TreeNewbeer/esp32c6-pico/output/antenna-28mm-comparison.png

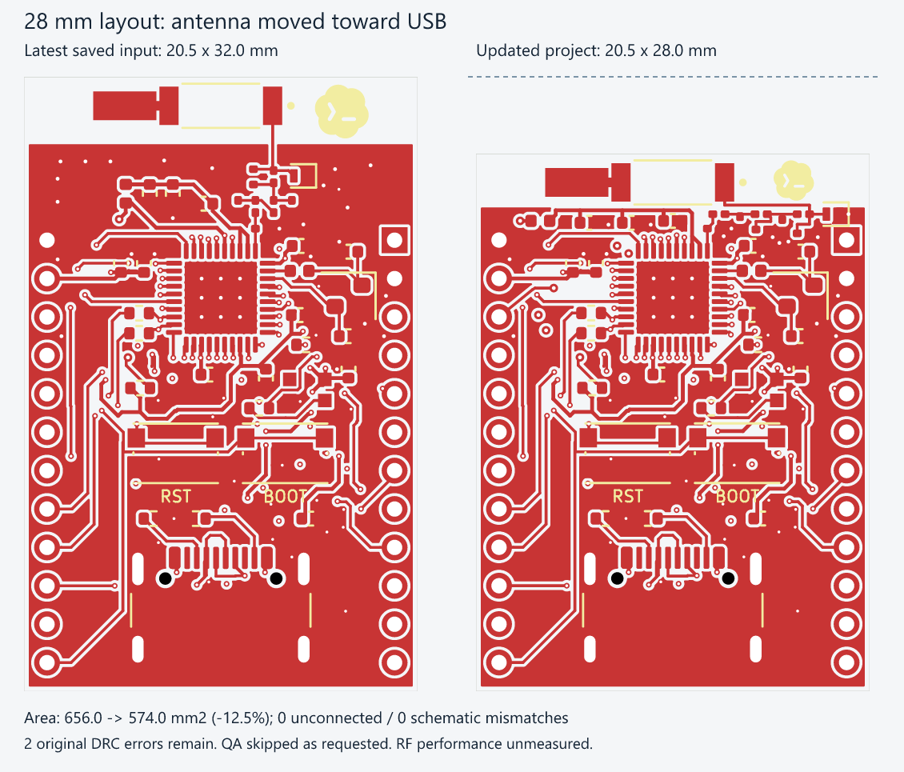
output/antenna-28mm-comparison.png
