TreeNewbeer/esp32c6-pico/output/antenna-layout-comparison.png

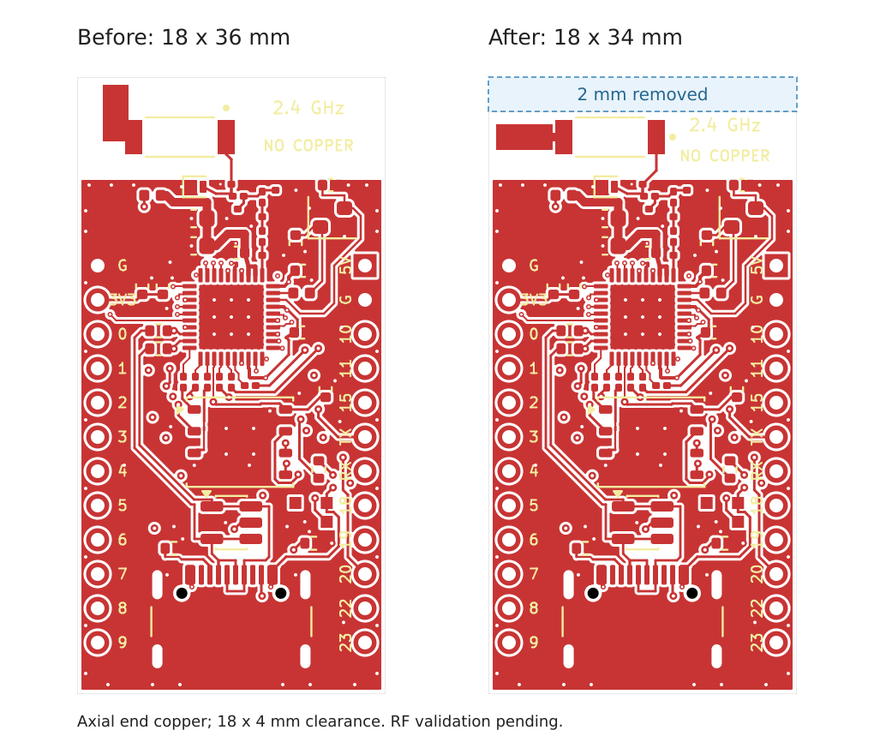
output/antenna-layout-comparison.png
