TreeNewbeer/esp32c6-pico/output/antenna-right-29mm-comparison.png

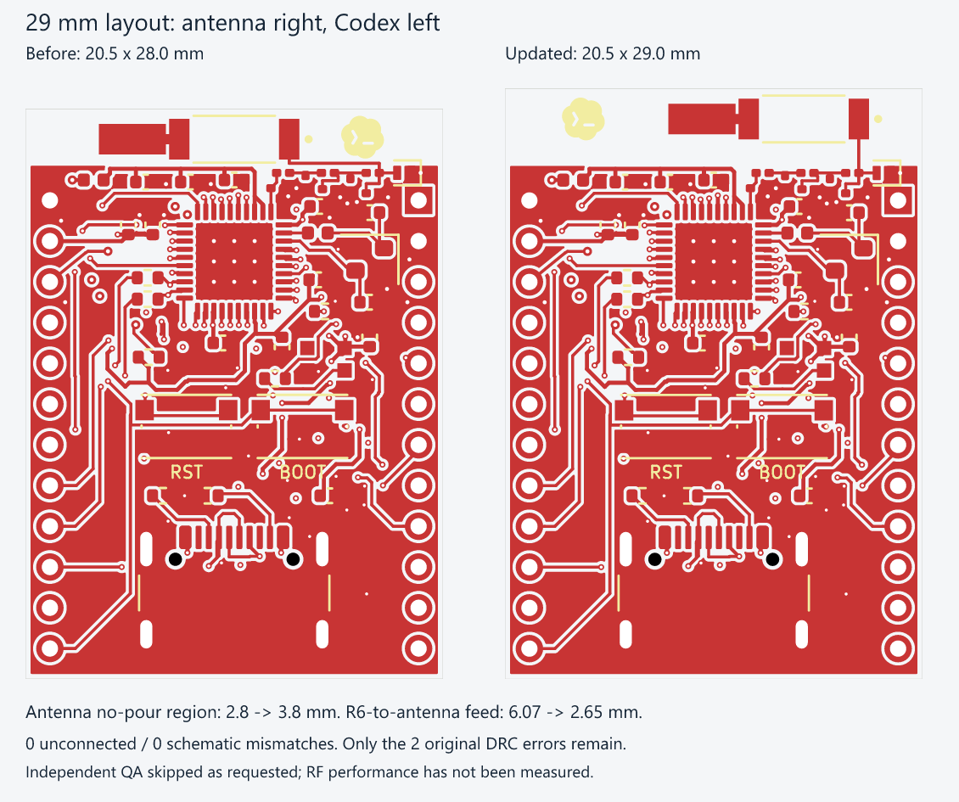
output/antenna-right-29mm-comparison.png
