TreeNewbeer/esp32c6-pico/output/board-3d-bottom.png

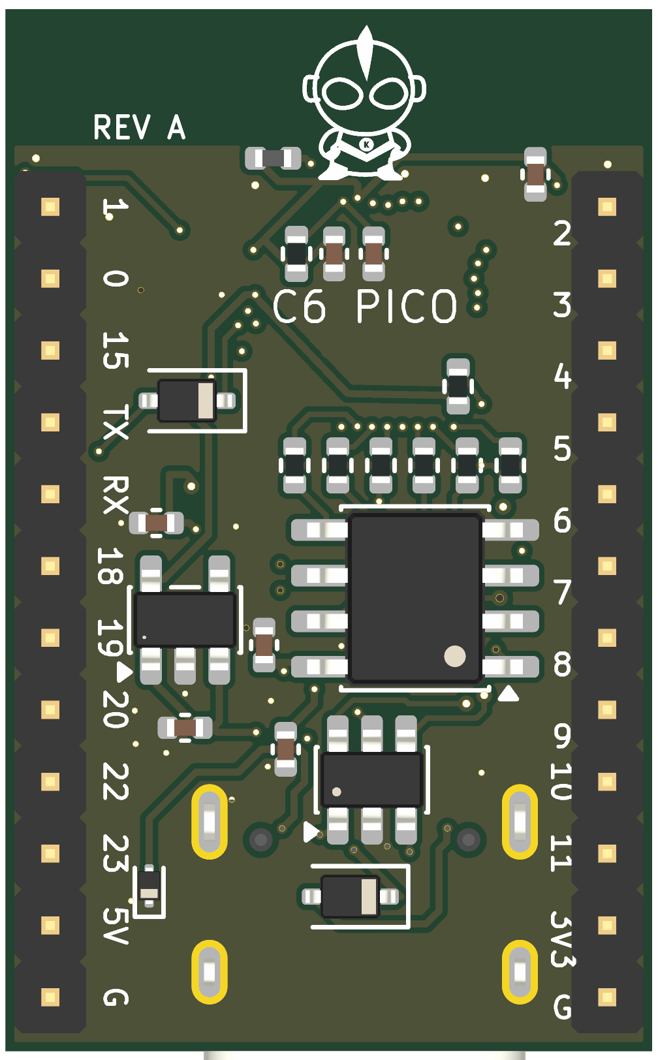
output/board-3d-bottom.png
