TreeNewbeer/esp32c6-pico/output/board-3d-top.png

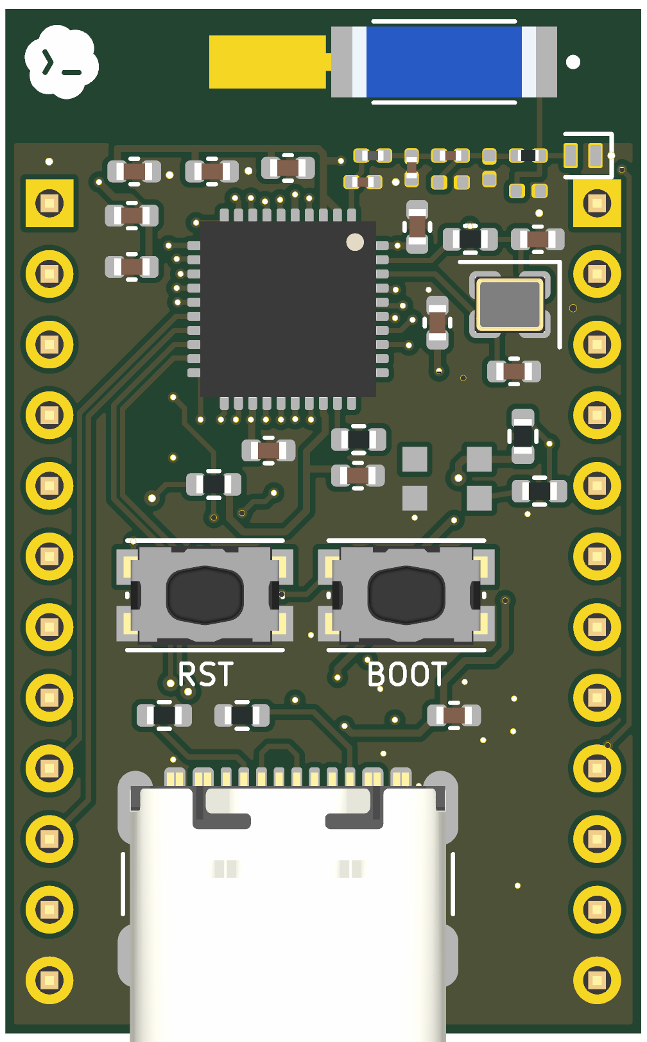
output/board-3d-top.png
