TreeNewbeer/esp32c6-pico/output/crystal-down-headers-comparison.png

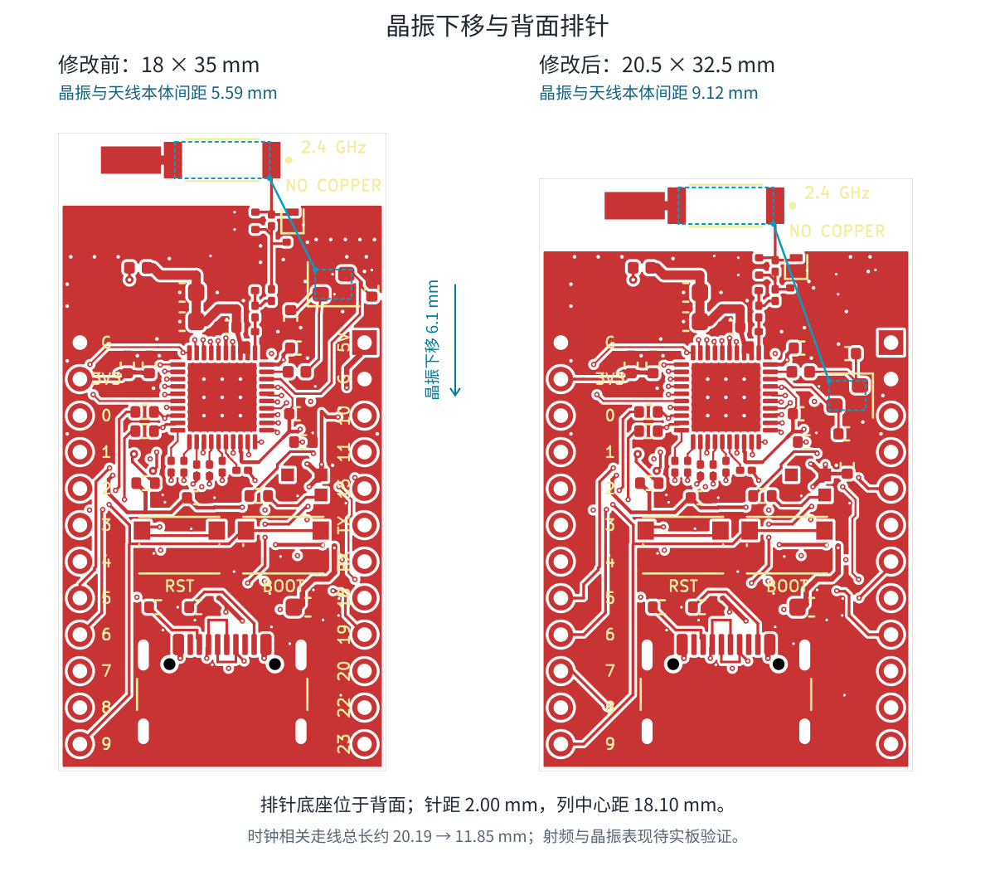
output/crystal-down-headers-comparison.png
