TreeNewbeer/esp32c6-pico/output/crystal-isolation-comparison.png

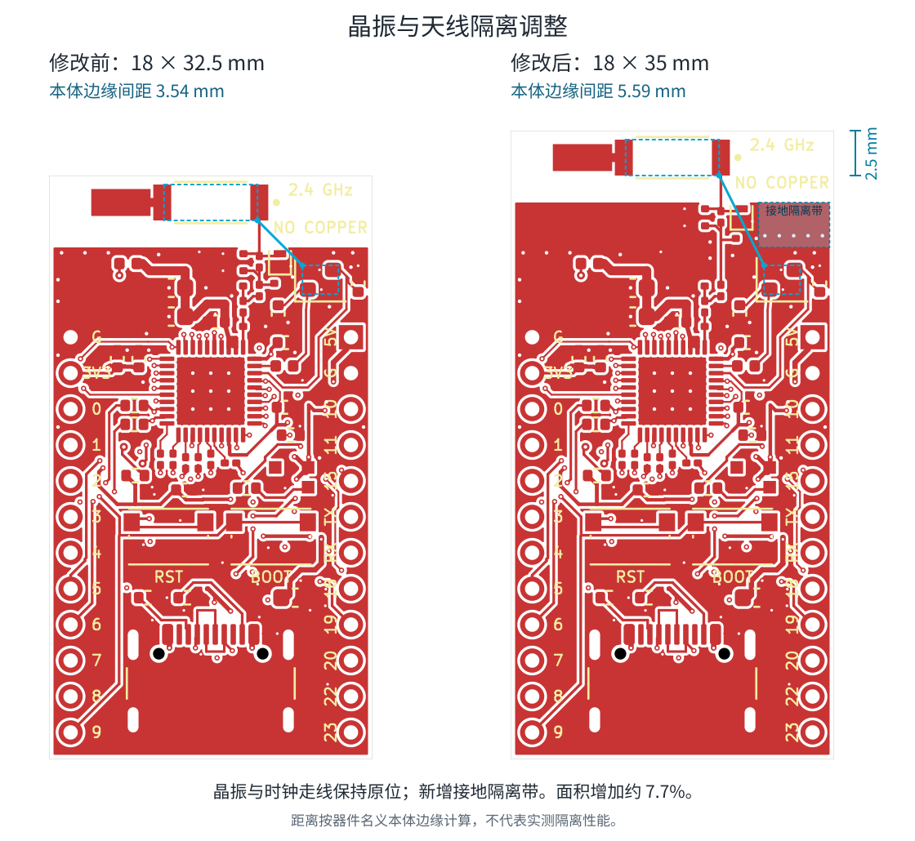
output/crystal-isolation-comparison.png
