TreeNewbeer/esp32c6-pico/output/layout-repack-comparison.png

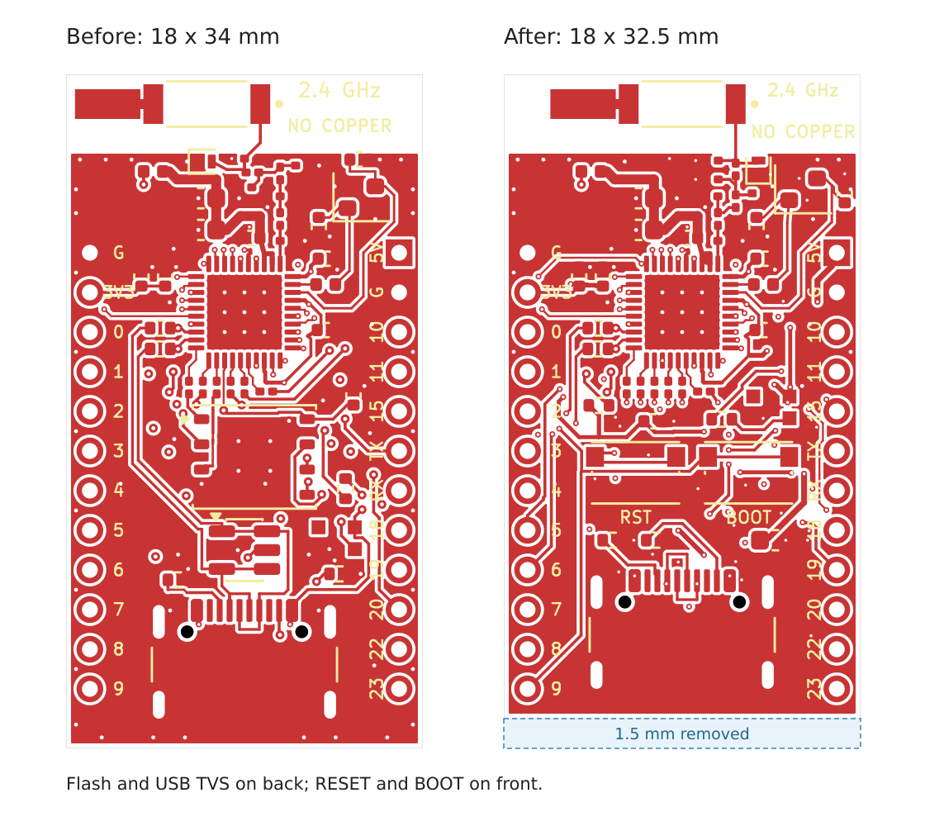
output/layout-repack-comparison.png
