TreeNewbeer/esp32c6-pico/output/pcb-back.png

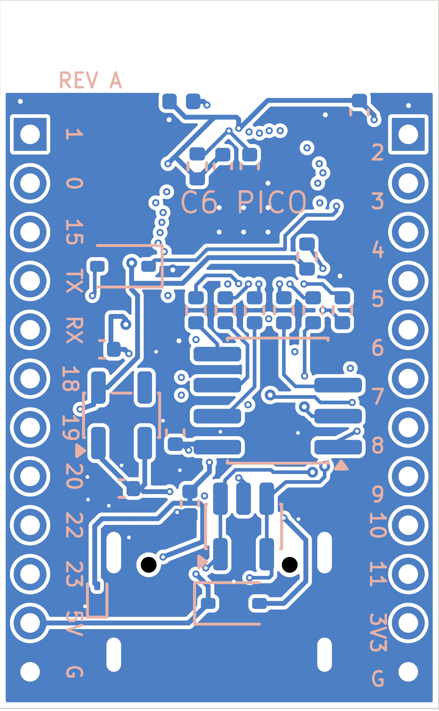
output/pcb-back.png
