TreeNewbeer/esp32c6-pico/output/pcb-front.png

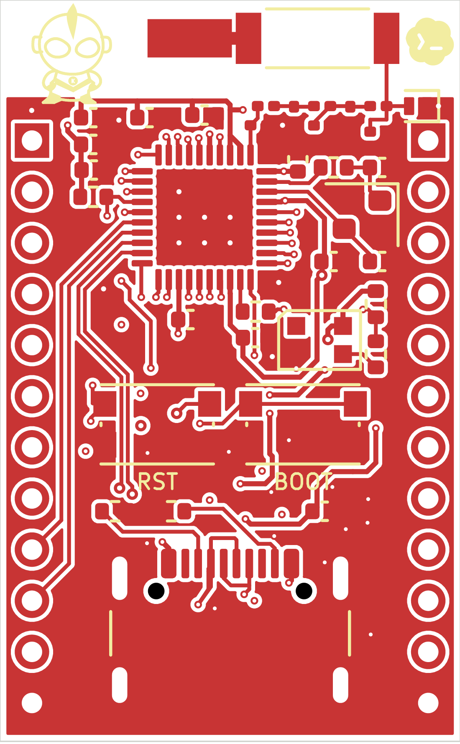
output/pcb-front.png
