TreeNewbeer/esp32c6-pico/output/rgb-diode-comparison.png

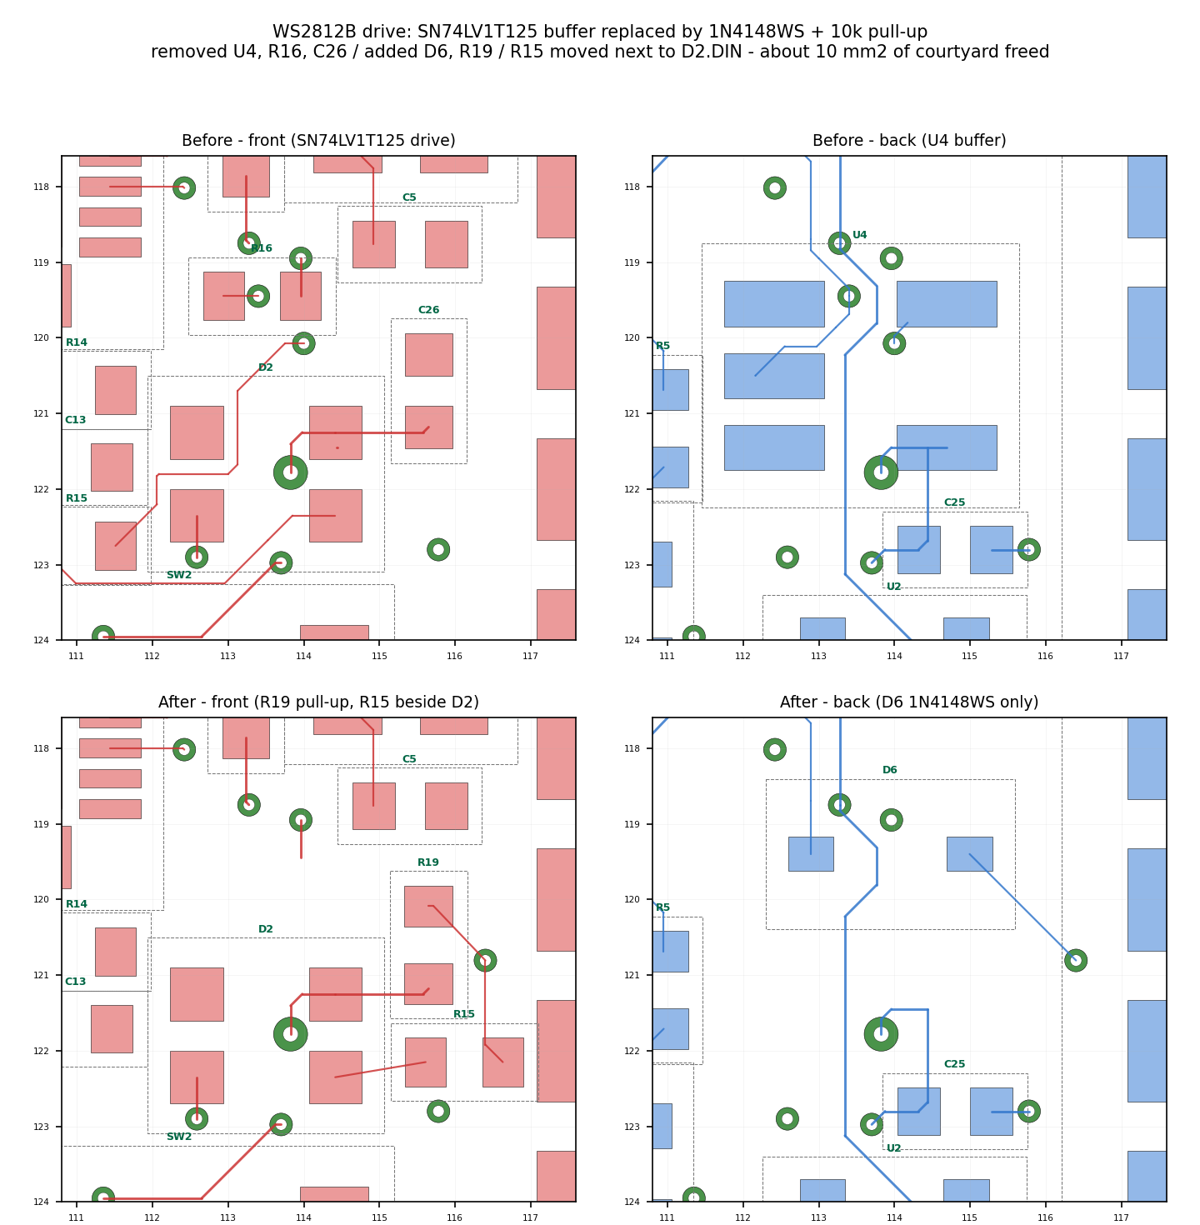
output/rgb-diode-comparison.png
