TreeNewbeer/esp32c6-pico/output/schematic/esp32-c6-pico-Power, USB and interfaces.png

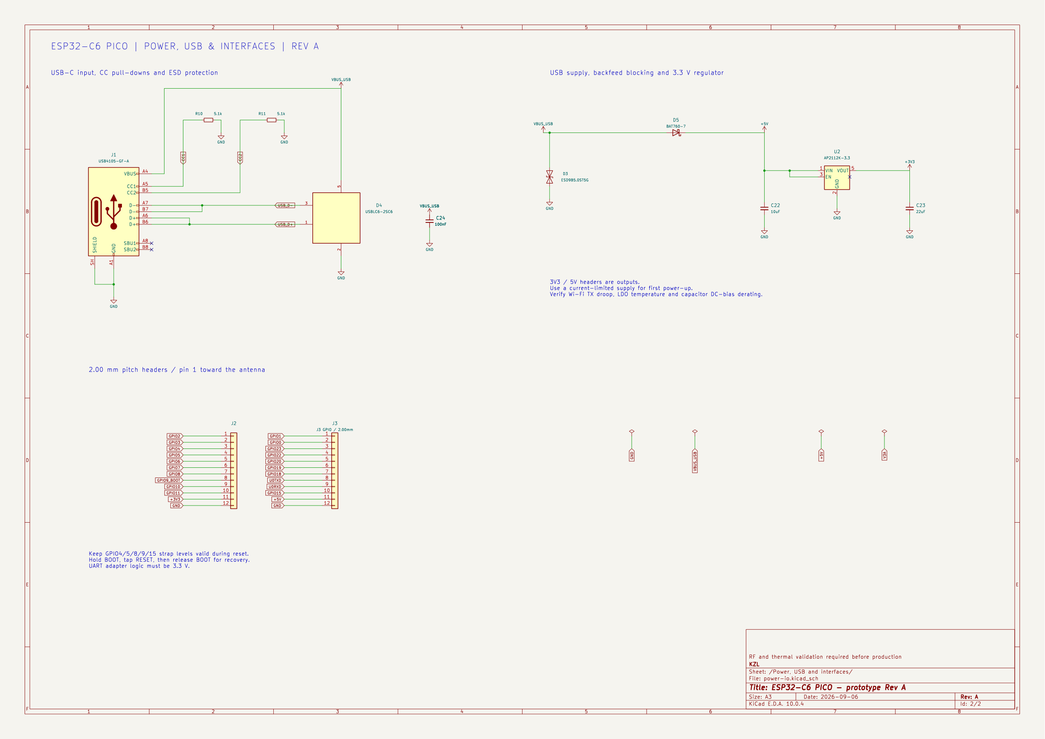
output/schematic/esp32-c6-pico-Power, USB and interfaces.png
