TreeNewbeer/esp32c6-pico/output/schematic/esp32-c6-pico.png

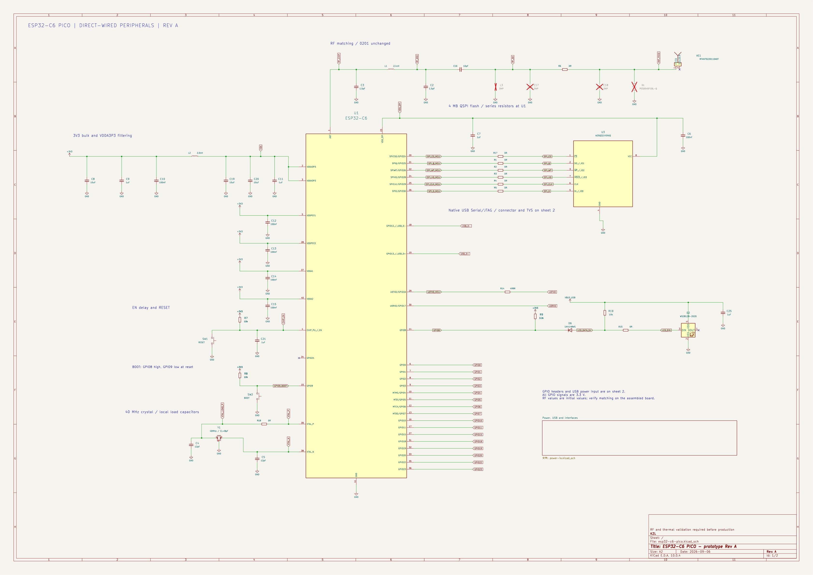
output/schematic/esp32-c6-pico.png
