TreeNewbeer/esp32c6-pico/output/schematic/rgb-gpio8.png

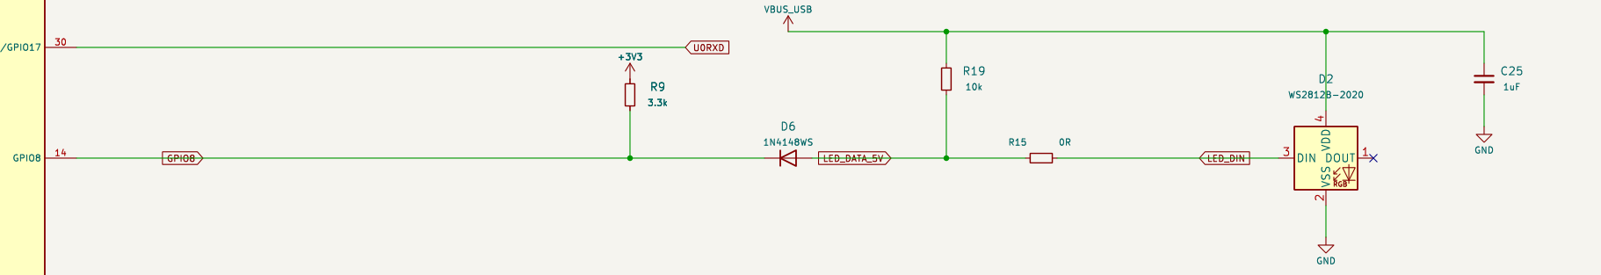
output/schematic/rgb-gpio8.png
