TreeNewbeer/esp32c6-pico/output/usb-buttons-centered-comparison.png

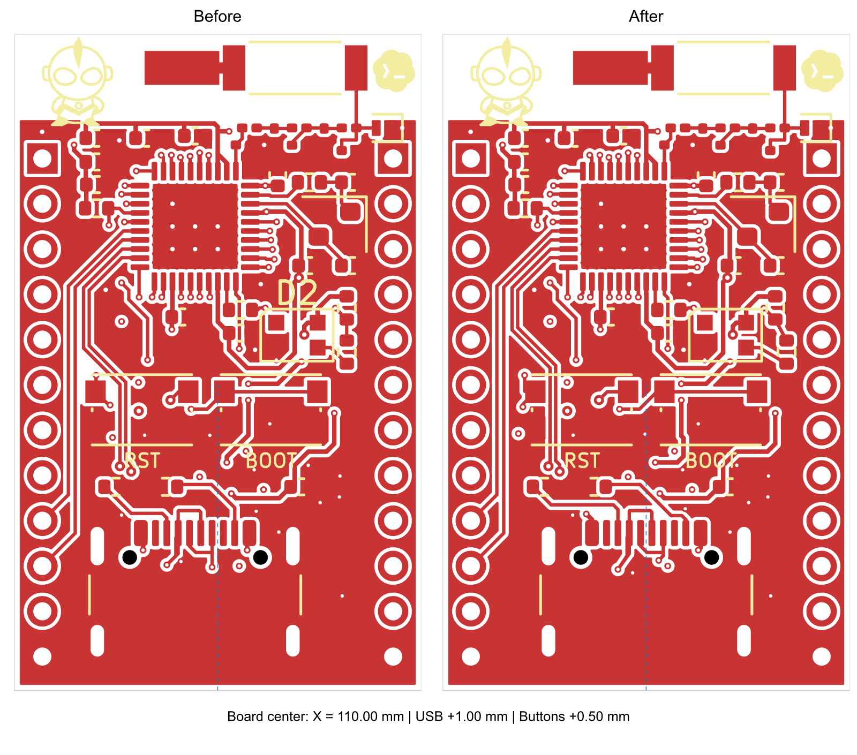
output/usb-buttons-centered-comparison.png
