TreeNewbeer/esp32c6-pico/output/usb-routing-comparison.png

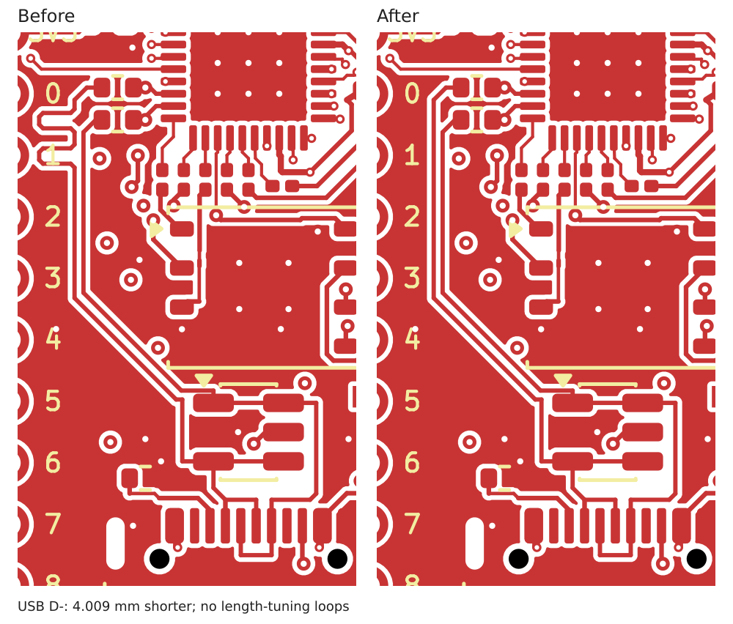
output/usb-routing-comparison.png
