TreeNewbeer/esp32c6-pico/output/width-20mm-comparison.png

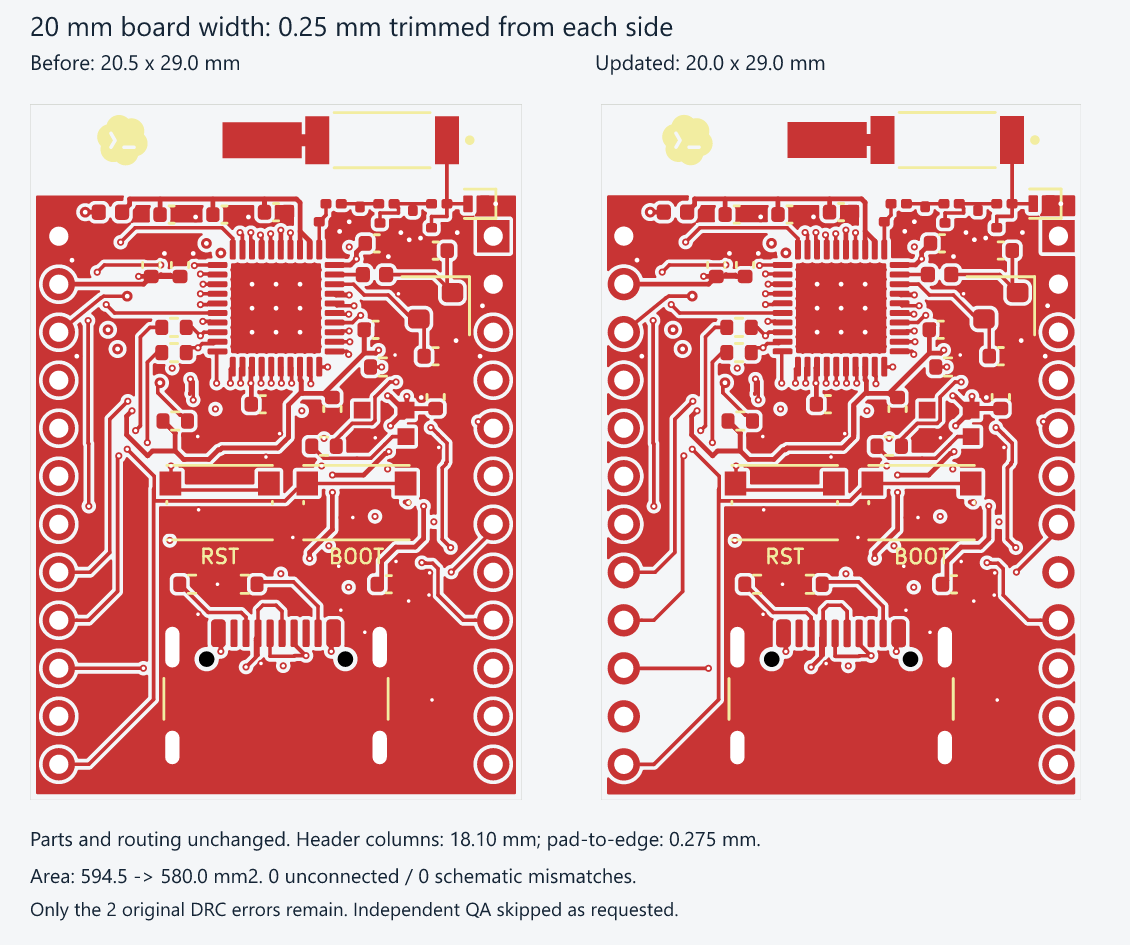
output/width-20mm-comparison.png
