TreeNewbeer/esp32c6-pico/output/assembly-back.png

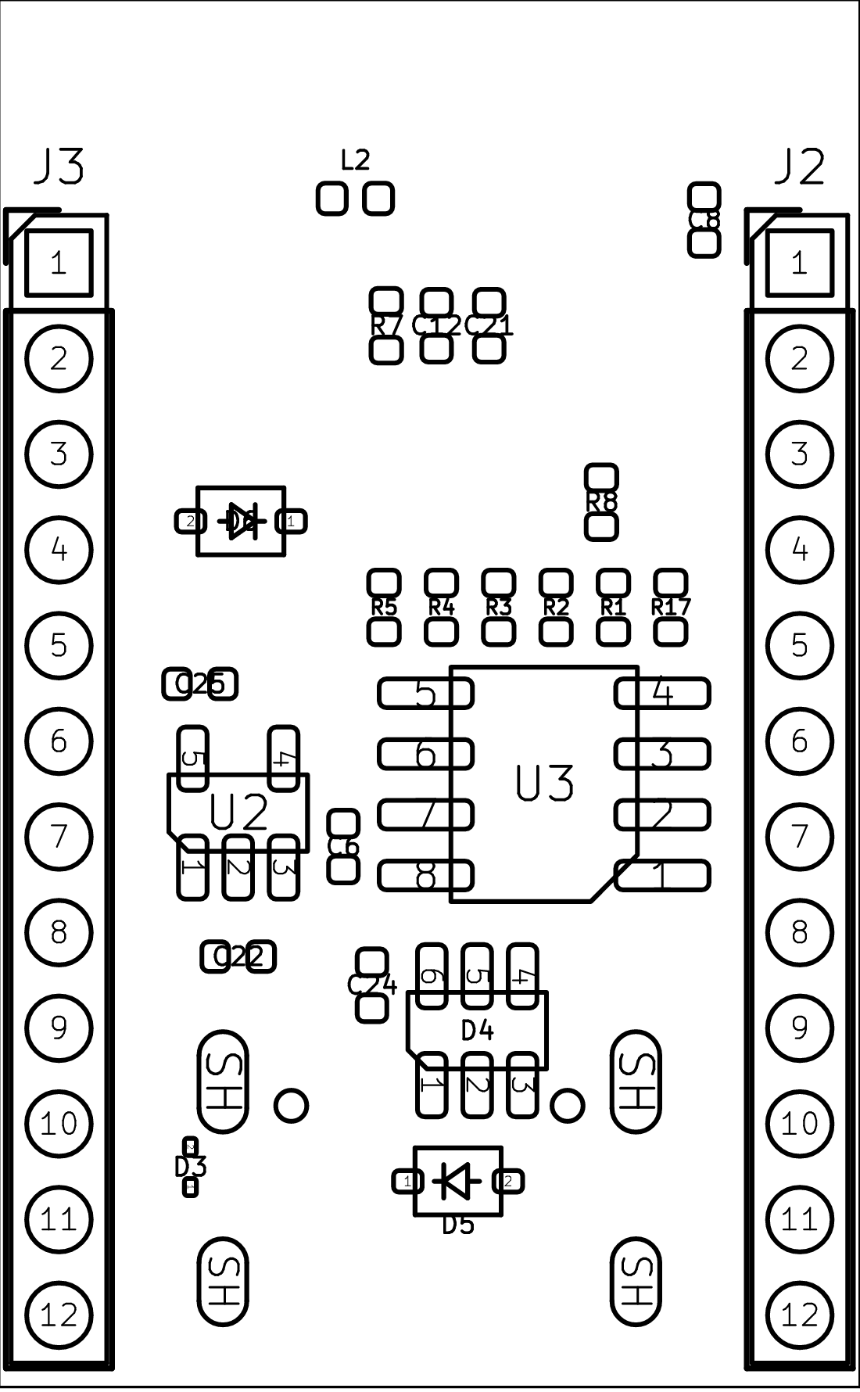
output/assembly-back.png
