TreeNewbeer/esp32c6-pico/output/assembly-front.png

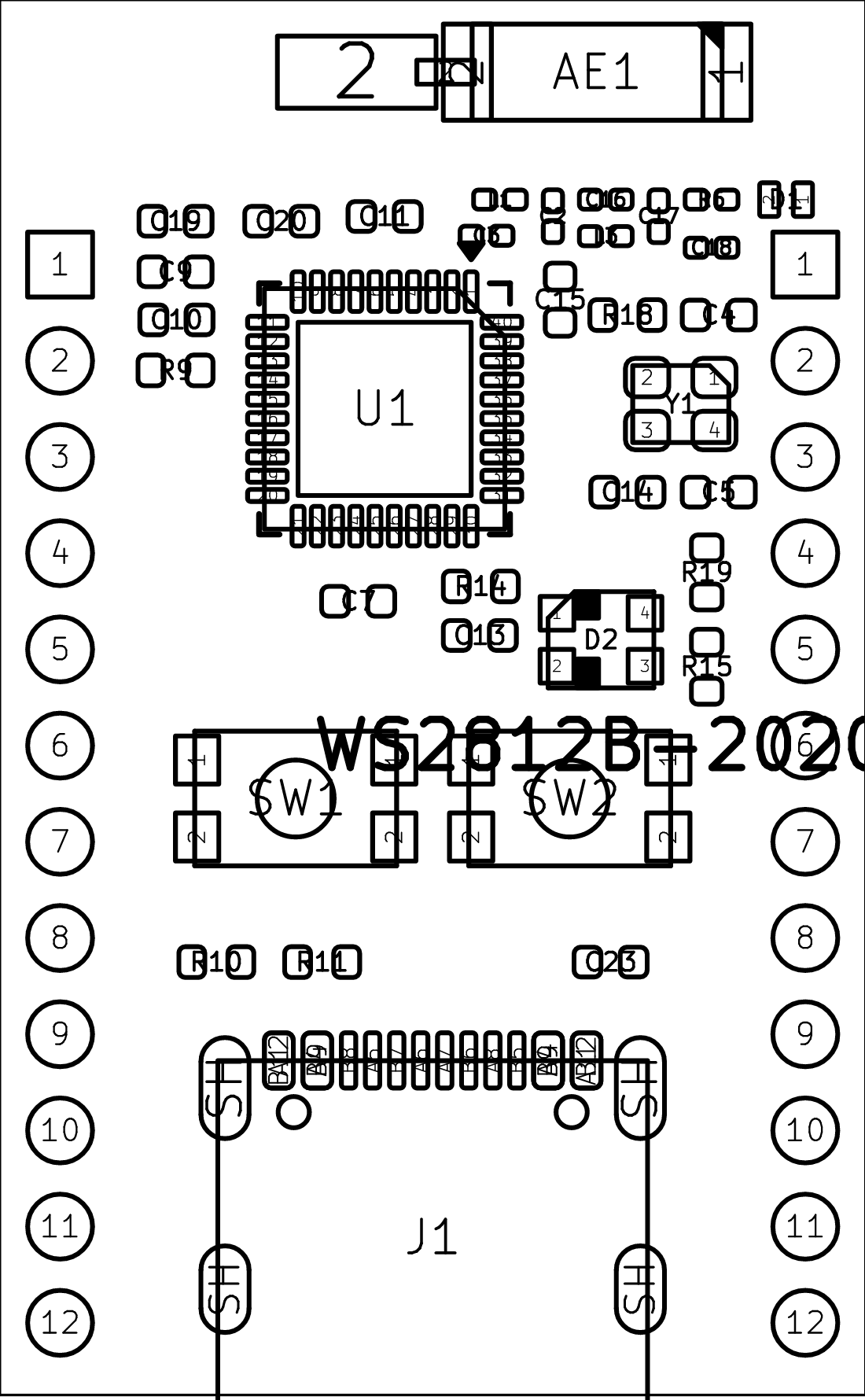
output/assembly-front.png
